KostelidisDev/EchoLite/assets/pcb/EchoLite/EchoLite.kicad_sch

## KiCad design assets/pcb/EchoLite/EchoLite.kicad_sch (2025-06-15)

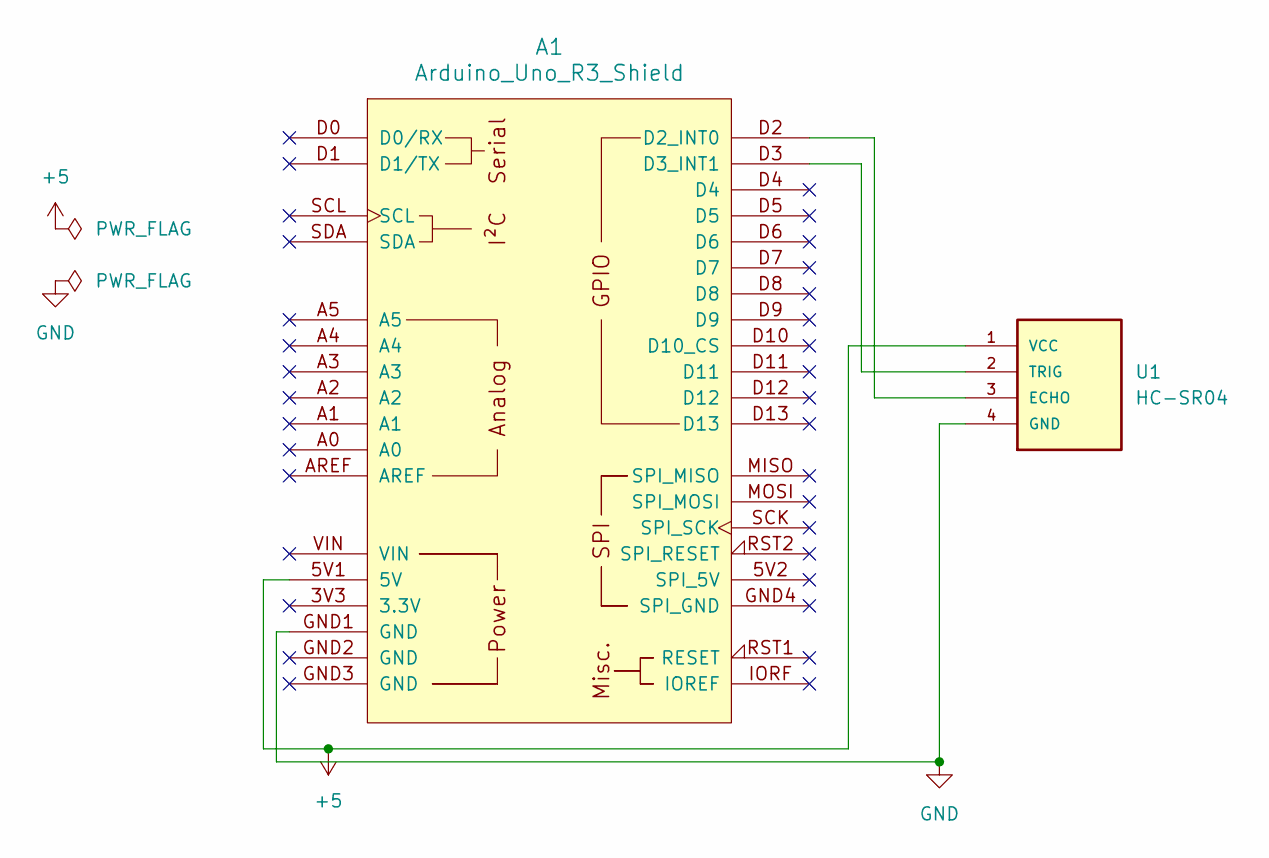
[picture p16: schematic EchoLite.kicad_sch]

Parts:
A1: Arduino_Uno_R3_Shield
U1: HC-SR04; XCVR_HC-SR04

Connections:
+5: A1.5V1 (5V), U1.1 (VCC)
GND: A1.GND1 (GND), U1.4 (GND)
unnamed: A1.D2 (D2_INT0), U1.3 (ECHO)
unnamed: A1.D3 (D3_INT1), U1.2 (TRIG)
